surgesg/tabulaRasa/tabularasa_src/software/tabulaRasa_Processing/data/about.png

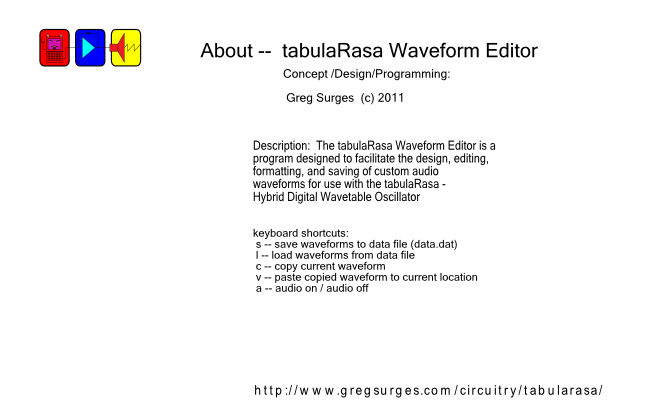
tabularasa_src/software/tabulaRasa_Processing/data/about.png
