surgesg/tabulaRasa/tabularasa_src/software/tabulaRasa_Processing/data/speaker.png

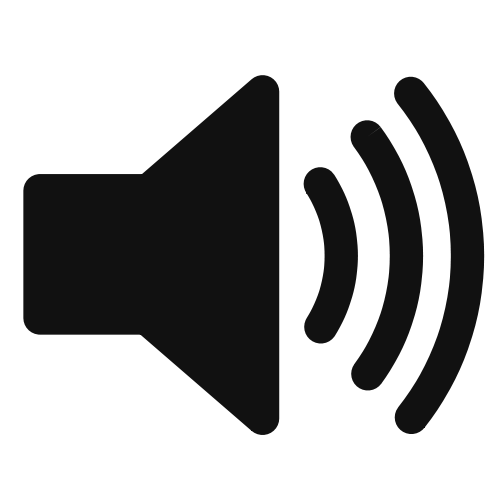
tabularasa_src/software/tabulaRasa_Processing/data/speaker.png
